ahaickTechnion/UMGT2026_AH/UMGT/00. PCB Boards/RPMSENSOR/sensordiagram2.png

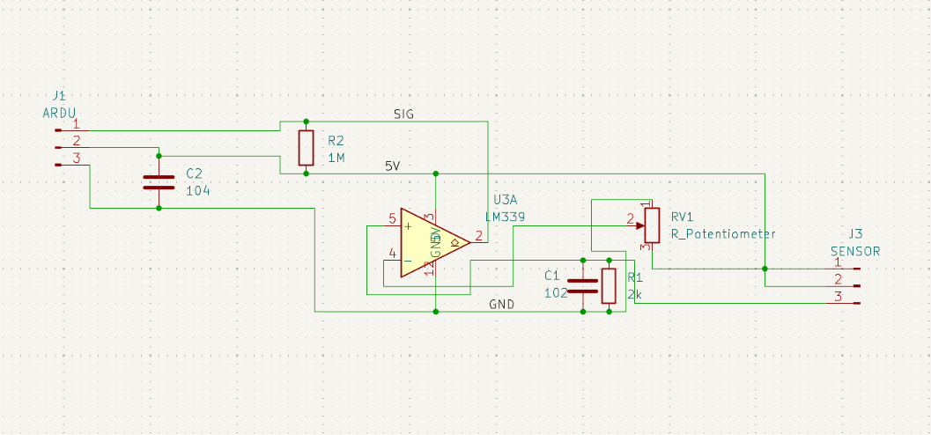
UMGT/00. PCB Boards/RPMSENSOR/sensordiagram2.png
