ahaickTechnion/UMGT2026_AH/UMGT/02. Documents/Betterevenbetter.png

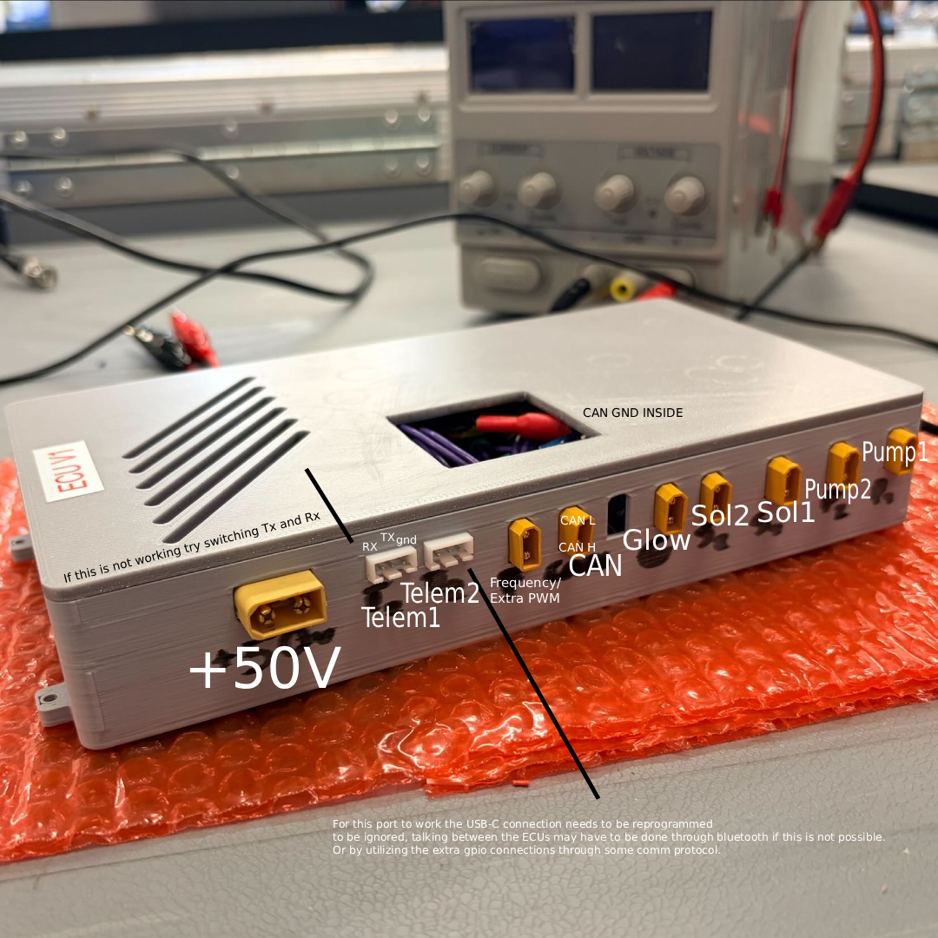
UMGT/02. Documents/Betterevenbetter.png
