ahaickTechnion/UMGT2026_AH/UMGT/02. Documents/ECUlayout.png

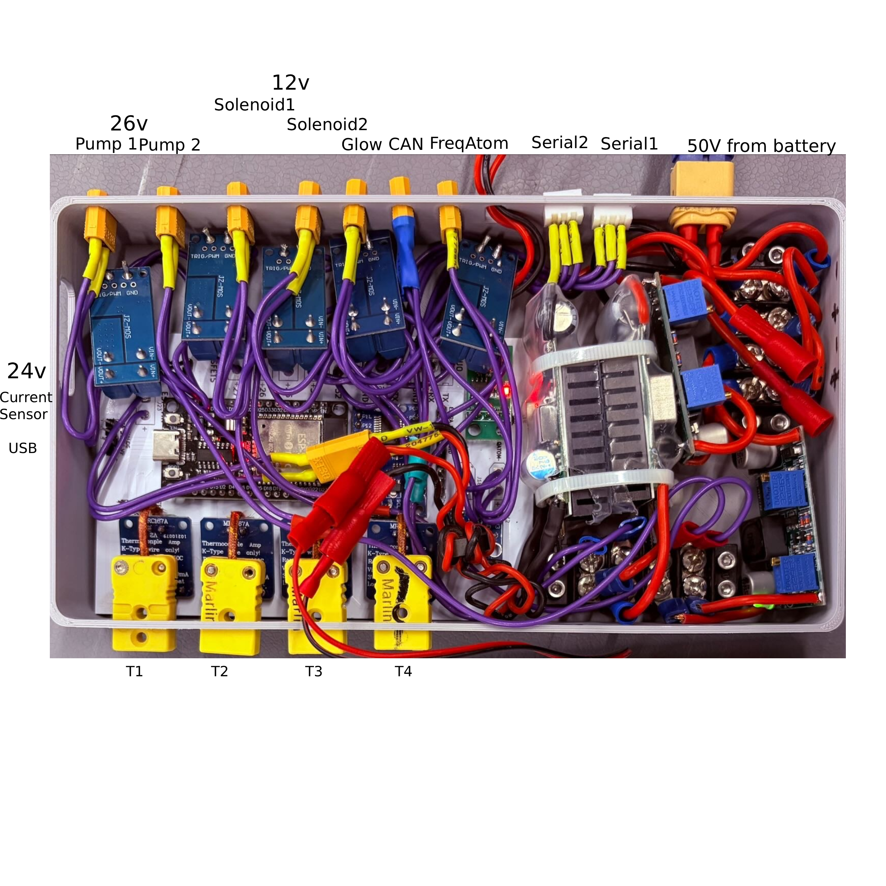
UMGT/02. Documents/ECUlayout.png
