ahaickTechnion/UMGT2026_AH/UMGT/02. Documents/Updated flat diagram.png

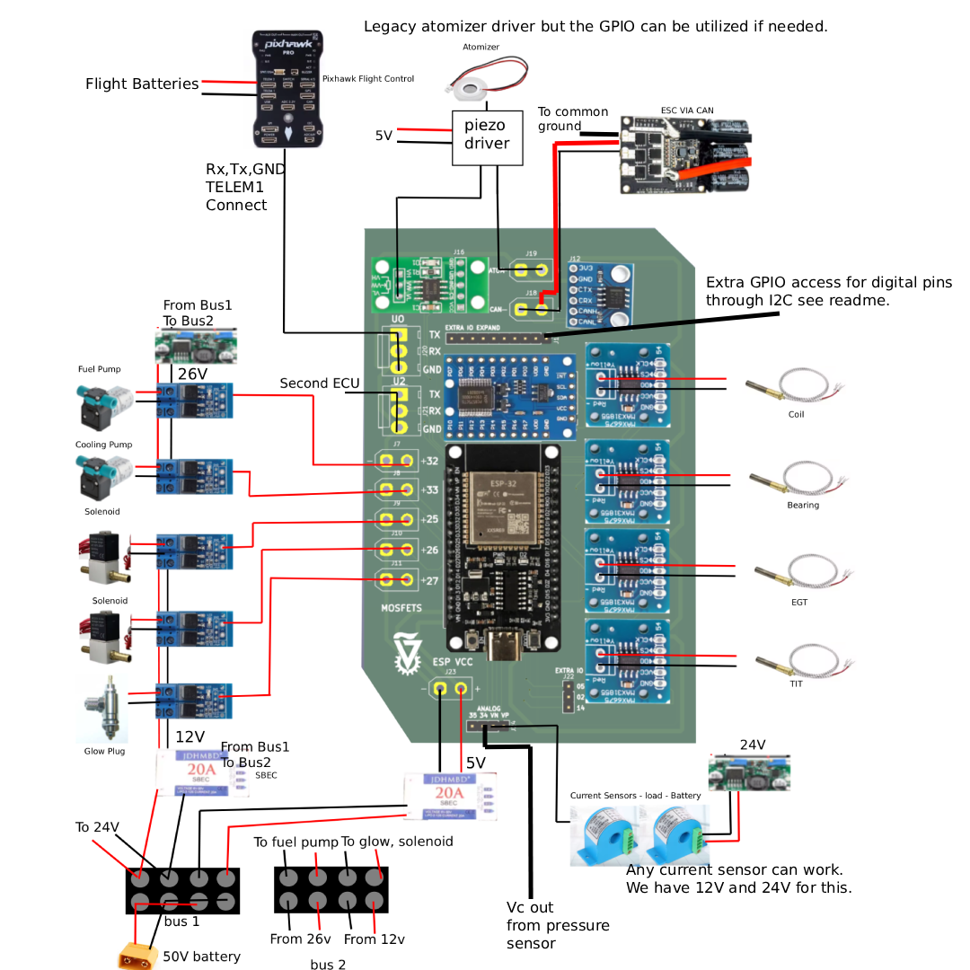
UMGT/02. Documents/Updated flat diagram.png
